coderkevin/mini-nes/buttons/log.py

import sys
import logging

def initLogger( logLevel, logFormat, logFile = None ):
    logger = logging.getLogger( 'NESButtons' )
    logger.setLevel( logLevel )

    logHandler = None

    if logFile:
        logHandler = logging.FileHandler( logFile )
    else:
        logHandler = logging.StreamHandler( sys.stdout )

    logHandler.setLevel( logLevel )
    logHandler.setFormatter( logging.Formatter( logFormat ) )
    logger.addHandler( logHandler )

    return logger
